Aphelion-Aerospace/psas-gps-rf-board/pubs/ethernet-circuits.pdf

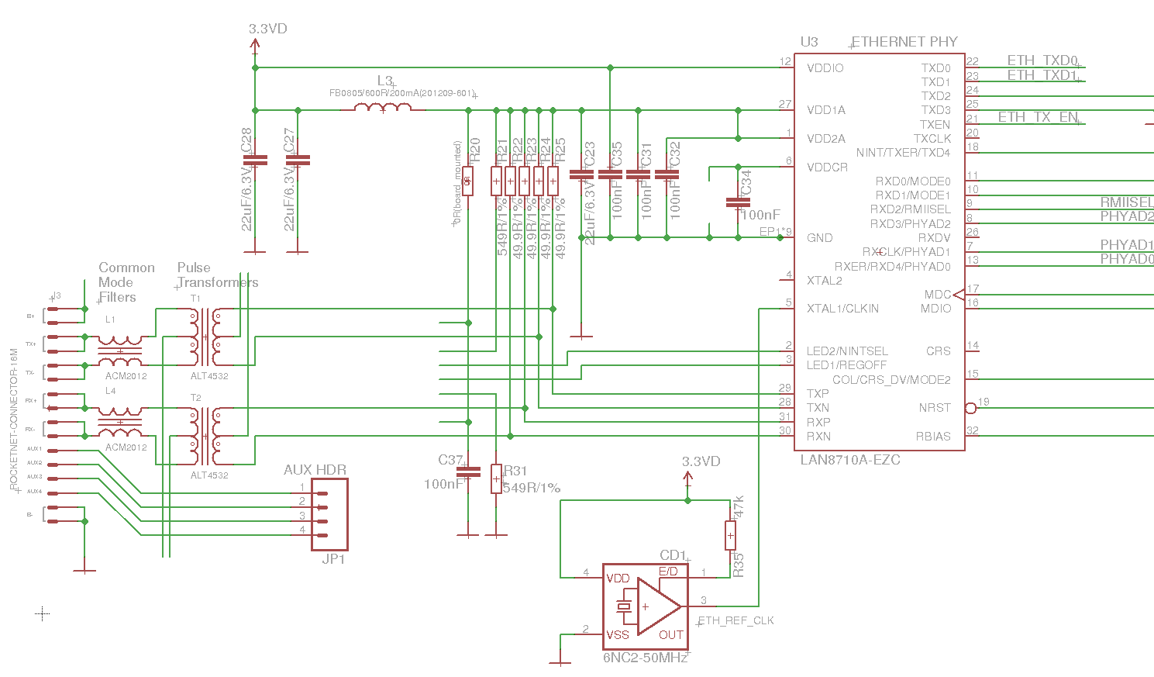
[picture p23: page 1]

GPS Board

Olimex E-407

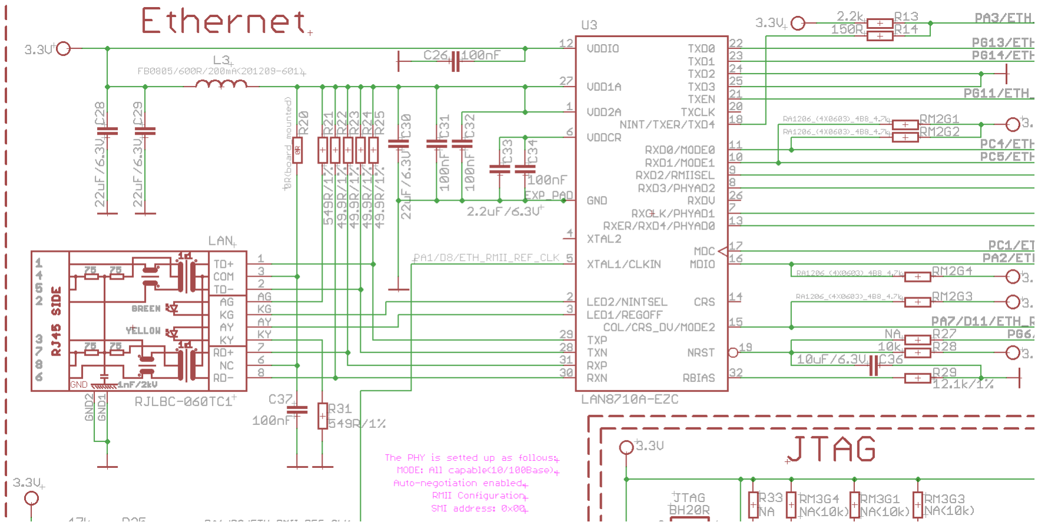
[picture p24: figure]

Rocketnet

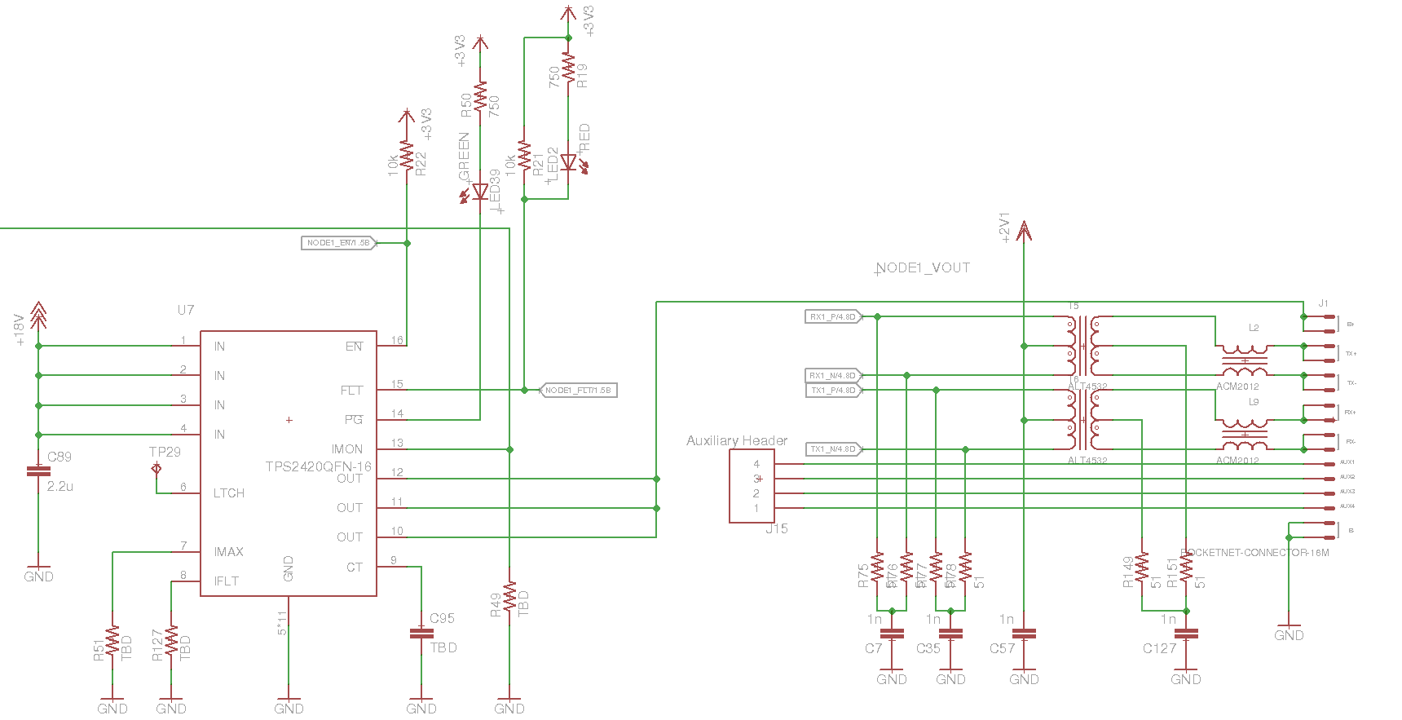
[picture p25: figure]
