Aphelion-Aerospace/psas-gps-rf-board/pubs/tcxo-7q-gps.pdf

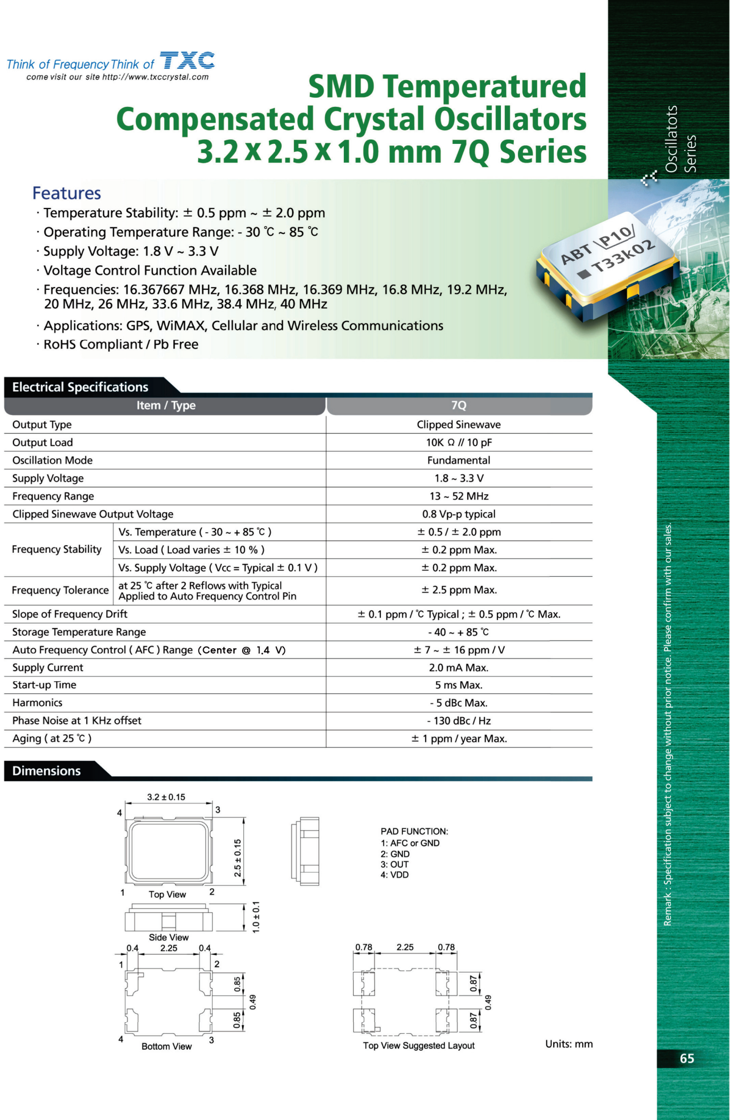
[picture p26: page 1]
