Aphelion-Aerospace/psas-gps-rf-board/pubs/con-samtec-swd-drawing.pdf

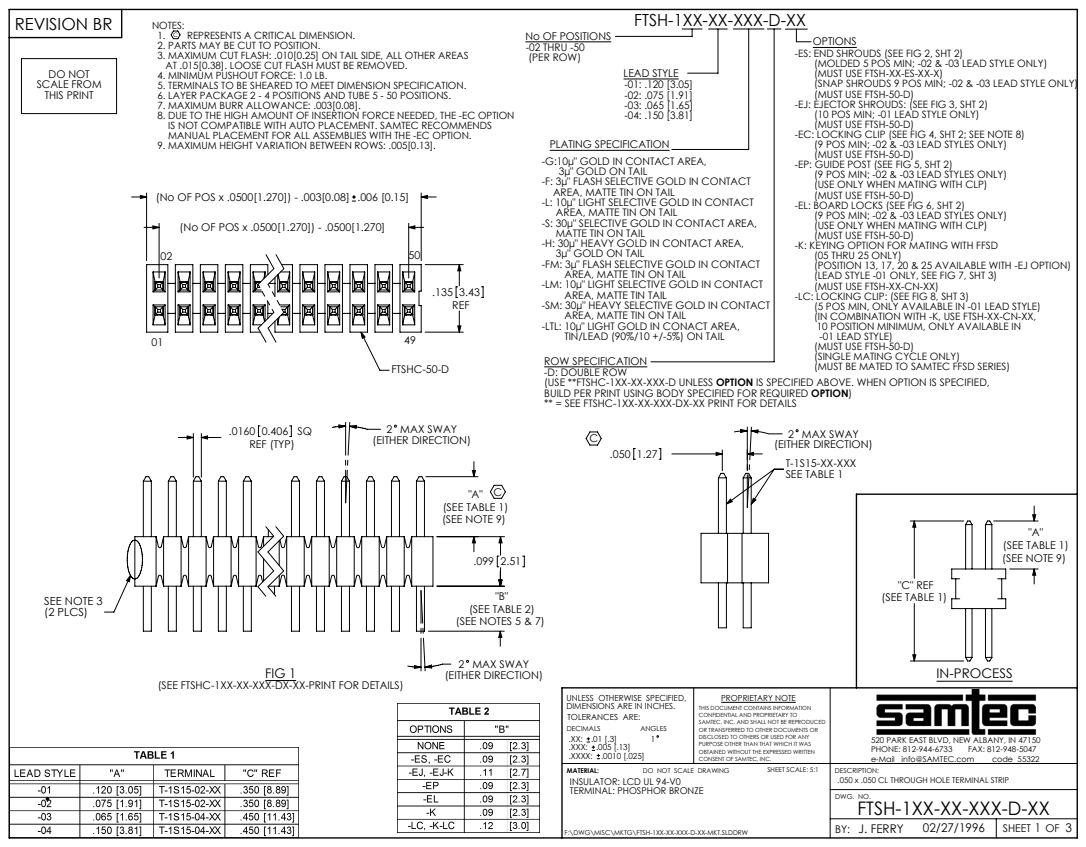
[picture p35: page 1]
DO NOT SCALE FROM THIS PRINT; LEAD STYLE -01: .120 [3.05] -02: .075 [1.91] -03: .065 [1.65] -04: .150 [3.81]; 2 MAX SWAY (EITHER DIRECTION) C; SEE TABLE 1; (SEE TABLE 1); "C" REF; (SEE NOTE 9); (SEE NOTES 5 & 7); (SEE TABLE 2); .0160 0.406 SQ REF (TYP); 2 MAX SWAY (EITHER DIRECTION); SEE NOTE 3 (2 PLCS); FIG 1; SHEET OF; J. FERRY 02/27/1996; SHEET SCALE: 5:1; PHONE: 812-944-6733; FAX: 812-948-5047; e-Mail info@SAMTEC.com; code 55322; REVISION BR

FTSH-1XX-XX-XXX-D-XX

NOTES:
1. REPRESENTS A CRITICAL DIMENSION.
2. PARTS MAY BE CUT TO POSITION.
3. MAXIMUM CUT FLASH: .010[0.25] ON TAIL SIDE, ALL OTHER AREAS
AT .015[0.38]. LOOSE CUT FLASH MUST BE REMOVED.
4. MINIMUM PUSHOUT FORCE: 1.0 LB.
5. TERMINALS TO BE SHEARED TO MEET DIMENSION SPECIFICATION.
6. LAYER PACKAGE 2 - 4 POSITIONS AND TUBE 5 - 50 POSITIONS.
7. MAXIMUM BURR ALLOWANCE: .003[0.08].
8. DUE TO THE HIGH AMOUNT OF INSERTION FORCE NEEDED, THE -EC OPTION
IS NOT COMPATIBLE WITH AUTO PLACEMENT. SAMTEC RECOMMENDS
MANUAL PLACEMENT FOR ALL ASSEMBLIES WITH THE -EC OPTION.
9. MAXIMUM HEIGHT VARIATION BETWEEN ROWS: .005[0.13].

No OF POSITIONS
-02 THRU -50
(PER ROW)

OPTIONS
-ES: END SHROUDS (SEE FIG 2, SHT 2)
(MOLDED 5 POS MIN; -02 & -03 LEAD STYLE ONLY)
(MUST USE FTSH-XX-ES-XX-X)
(SNAP SHROUDS 9 POS MIN; -02 & -03 LEAD STYLE ONLY)
(MUST USE FTSH-50-D)
-EJ: EJECTOR SHROUDS: (SEE FIG 3, SHT 2)
(10 POS MIN; -01 LEAD STYLE ONLY)
-EC: LOCKING CLIP (SEE FIG 4, SHT 2; SEE NOTE 8)
(9 POS MIN; -02 & -03 LEAD STYLES ONLY)
-EP: GUIDE POST (SEE FIG 5, SHT 2)
(USE ONLY WHEN MATING WITH CLP)
-EL: BOARD LOCKS (SEE FIG 6, SHT 2)
-K: KEYING OPTION FOR MATING WITH FFSD
(05 THRU 25 ONLY)
(POSITION 13, 17, 20 & 25 AVAILABLE WITH -EJ OPTION)
(LEAD STYLE -01 ONLY, SEE FIG 7, SHT 3)
(MUST USE FTSH-XX-CN-XX)
-LC: LOCKING CLIP: (SEE FIG 8, SHT 3)
(5 POS MIN, ONLY AVAILABLE IN -01 LEAD STYLE)
(IN COMBINATION WITH -K, USE FTSH-XX-CN-XX,
10 POSITION MINIMUM, ONLY AVAILABLE IN
-01 LEAD STYLE)
(SINGLE MATING CYCLE ONLY)
(MUST BE MATED TO SAMTEC FFSD SERIES)

PLATING SPECIFICATION
-G:10µ" GOLD IN CONTACT AREA,
3µ" GOLD ON TAIL
-F: 3µ" FLASH SELECTIVE GOLD IN CONTACT
AREA, MATTE TIN ON TAIL
-L: 10µ" LIGHT SELECTIVE GOLD IN CONTACT
-S: 30µ" SELECTIVE GOLD IN CONTACT AREA,
MATTE TIN ON TAIL
-H: 30µ" HEAVY GOLD IN CONTACT AREA,
-FM: 3µ" FLASH SELECTIVE GOLD IN CONTACT
-LM: 10µ" LIGHT SELECTIVE GOLD IN CONTACT
AREA, MATTE TIN TAIL
-SM: 30µ" HEAVY SELECTIVE GOLD IN CONTACT
-LTL: 10µ" LIGHT GOLD IN CONACT AREA,
TIN/LEAD (90%/10 +/-5%) ON TAIL
ROW SPECIFICATION
-D: DOUBLE ROW
(USE **FTSHC-1XX-XX-XXX-D UNLESS OPTION IS SPECIFIED ABOVE. WHEN OPTION IS SPECIFIED,
BUILD PER PRINT USING BODY SPECIFIED FOR REQUIRED OPTION)
** = SEE FTSHC-1XX-XX-XXX-DX-XX PRINT FOR DETAILS

(No OF POS x .0500[1.270]) - .003[0.08] .006 [0.15]

(No OF POS x .0500[1.270]) - .0500[1.270]

(SEE FTSHC-1XX-XX-XXX-DX-XX-PRINT FOR DETAILS)

UNLESS OTHERWISE SPECIFIED,
DIMENSIONS ARE IN INCHES.
TOLERANCES ARE:
.XXX: .005 [.13]
.XXXX: .0010 [.025]
MATERIAL:
INSULATOR: LCD UL 94-V0
TERMINAL: PHOSPHOR BRONZE

PROPRIETARY NOTE
THIS DOCUMENT CONTAINS INFORMATION
CONFIDENTIAL AND PROPRIETARY TO
SAMTEC, INC. AND SHALL NOT BE REPRODUCED
OR TRANSFERRED TO OTHER DOCUMENTS OR
DISCLOSED TO OTHERS OR USED FOR ANY
PURPOSE OTHER THAN THAT WHICH IT WAS
OBTAINED WITHOUT THE EXPRESSED WRITTEN
CONSENT OF SAMTEC, INC.

520 PARK EAST BLVD, NEW ALBANY, IN 47150
FTSH-1XX-XX-XXX-D-XX DWG. NO.

DO NOT SCALE DRAWING

DESCRIPTION:
.050 x .050 CL THROUGH HOLE TERMINAL STRIP

F:\DWG\MISC\MKTG\FTSH-1XX-XX-XXX-D-XX-MKT.SLDDRW

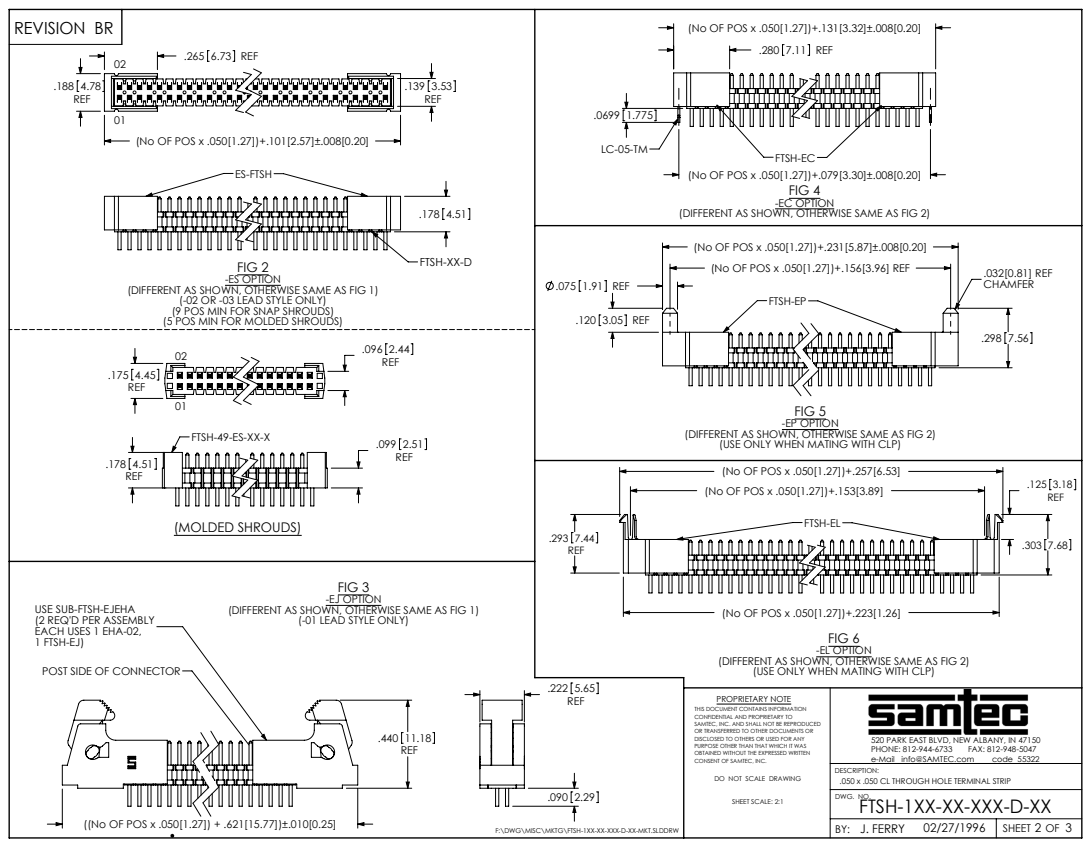
[picture p36: page 2]
(No OF POS x .050[1.27])+.101[2.57]±.008[0.20]; FIG 2 -ES OPTION; REF .178; (MOLDED SHROUDS); FIG 6 -EL OPTION; .032[0.81] REF; J. FERRY 02/27/1996; SHEET SCALE: 2:1; PHONE: 812-944-6733; FAX: 812-948-5047; e-Mail info@SAMTEC.com; code 55322

(No OF POS x .050[1.27])+.131[3.32]±.008[0.20]

(No OF POS x .050[1.27])+.079[3.30]±.008[0.20]

FIG 4 -EC OPTION (DIFFERENT AS SHOWN, OTHERWISE SAME AS FIG 2)

(No OF POS x .050[1.27])+.231[5.87]±.008[0.20]
(No OF POS x .050[1.27])+.156[3.96] REF

(DIFFERENT AS SHOWN, OTHERWISE SAME AS FIG 1)

(-02 OR -03 LEAD STYLE ONLY)
(9 POS MIN FOR SNAP SHROUDS)
(5 POS MIN FOR MOLDED SHROUDS)

FIG 5 -EP OPTION (DIFFERENT AS SHOWN, OTHERWISE SAME AS FIG 2) (USE ONLY WHEN MATING WITH CLP)

FTSH-49-ES-XX-X

(No OF POS x .050[1.27])+.257[6.53]
(No OF POS x .050[1.27])+.153[3.89]

FIG 3
-EJ OPTION
(-01 LEAD STYLE ONLY)

USE SUB-FTSH-EJEHA
(2 REQ'D PER ASSEMBLY
EACH USES 1 EHA-02,
1 FTSH-EJ)

(No OF POS x .050[1.27])+.223[1.26]

(DIFFERENT AS SHOWN, OTHERWISE SAME AS FIG 2)
(USE ONLY WHEN MATING WITH CLP)

POST SIDE OF CONNECTOR

PROPRIETARY NOTE
THIS DOCUMENT CONTAINS INFORMATION
CONFIDENTIAL AND PROPRIETARY TO
SAMTEC, INC. AND SHALL NOT BE REPRODUCED
OR TRANSFERRED TO OTHER DOCUMENTS OR
DISCLOSED TO OTHERS OR USED FOR ANY
PURPOSE OTHER THAN THAT WHICH IT WAS
OBTAINED WITHOUT THE EXPRESSED WRITTEN
CONSENT OF SAMTEC, INC.
DO NOT SCALE DRAWING

520 PARK EAST BLVD, NEW ALBANY, IN 47150

((No OF POS x .050[1.27]) + .621[15.77])±.010[0.25]

F:\DWG\MISC\MKTG\FTSH-1XX-XX-XXX-D-XX-MKT.SLDDRW

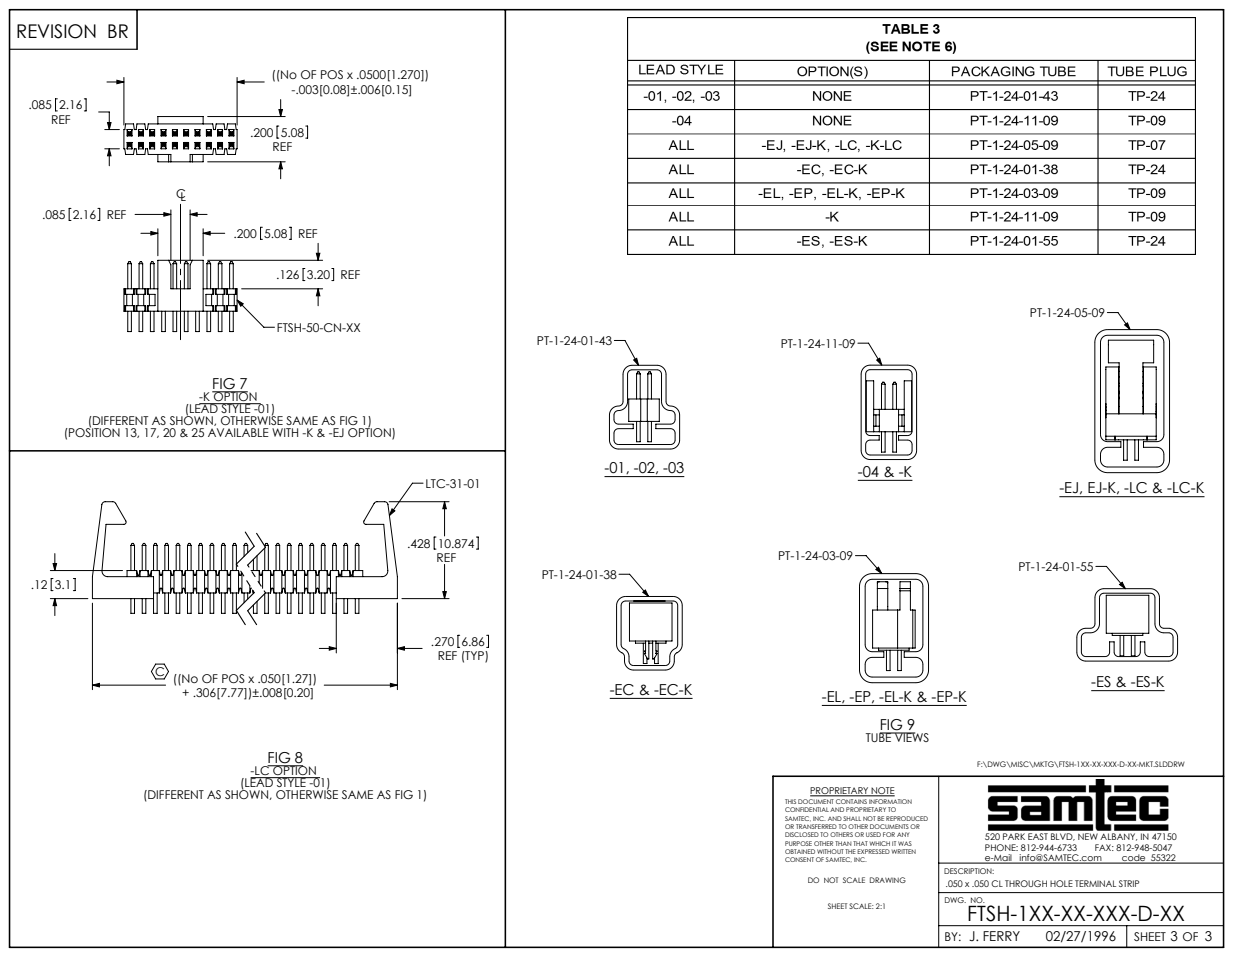
[picture p37: page 3]
FIG 7 -K OPTION (LEAD STYLE -01); ((No OF POS x .050[1.27]) + .306[7.77])±.008[0.20]; REF (TYP); FIG 8 -LC OPTION (LEAD STYLE -01); J. FERRY; SHEET SCALE: 2:1; PHONE: 812-944-6733; FAX: 812-948-5047; e-Mail info@SAMTEC.com; code 55322

((No OF POS x .0500[1.270])

FTSH-50-CN-XX

(DIFFERENT AS SHOWN, OTHERWISE SAME AS FIG 1)
(POSITION 13, 17, 20 & 25 AVAILABLE WITH -K & -EJ OPTION)

FIG 9
TUBE VIEWS

F:\DWG\MISC\MKTG\FTSH-1XX-XX-XXX-D-XX-MKT.SLDDRW

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

520 PARK EAST BLVD, NEW ALBANY, IN 47150
