Aphelion-Aerospace/psas-gps-rf-board/pubs/max2769/MAX2769-PACKAGE-21-0140.PDF

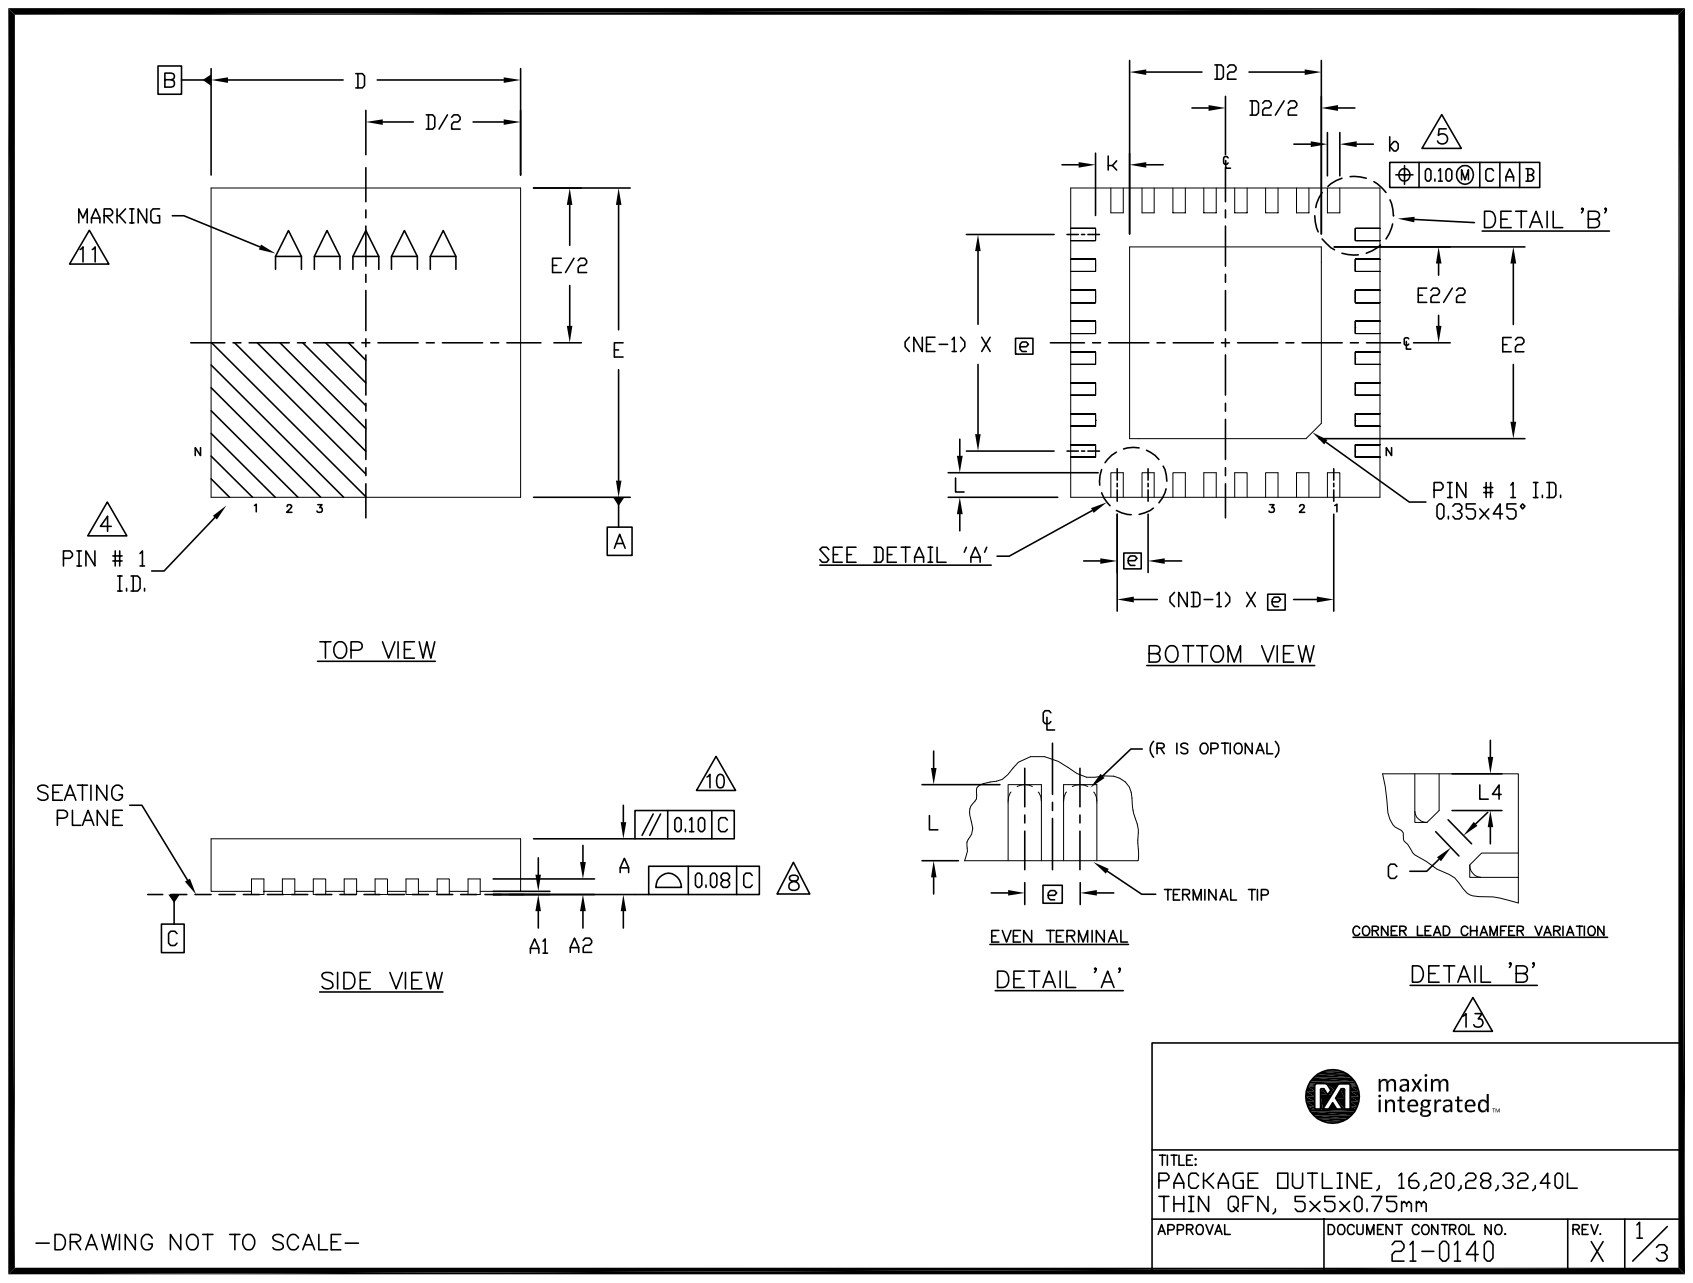
[picture p38: page 1]

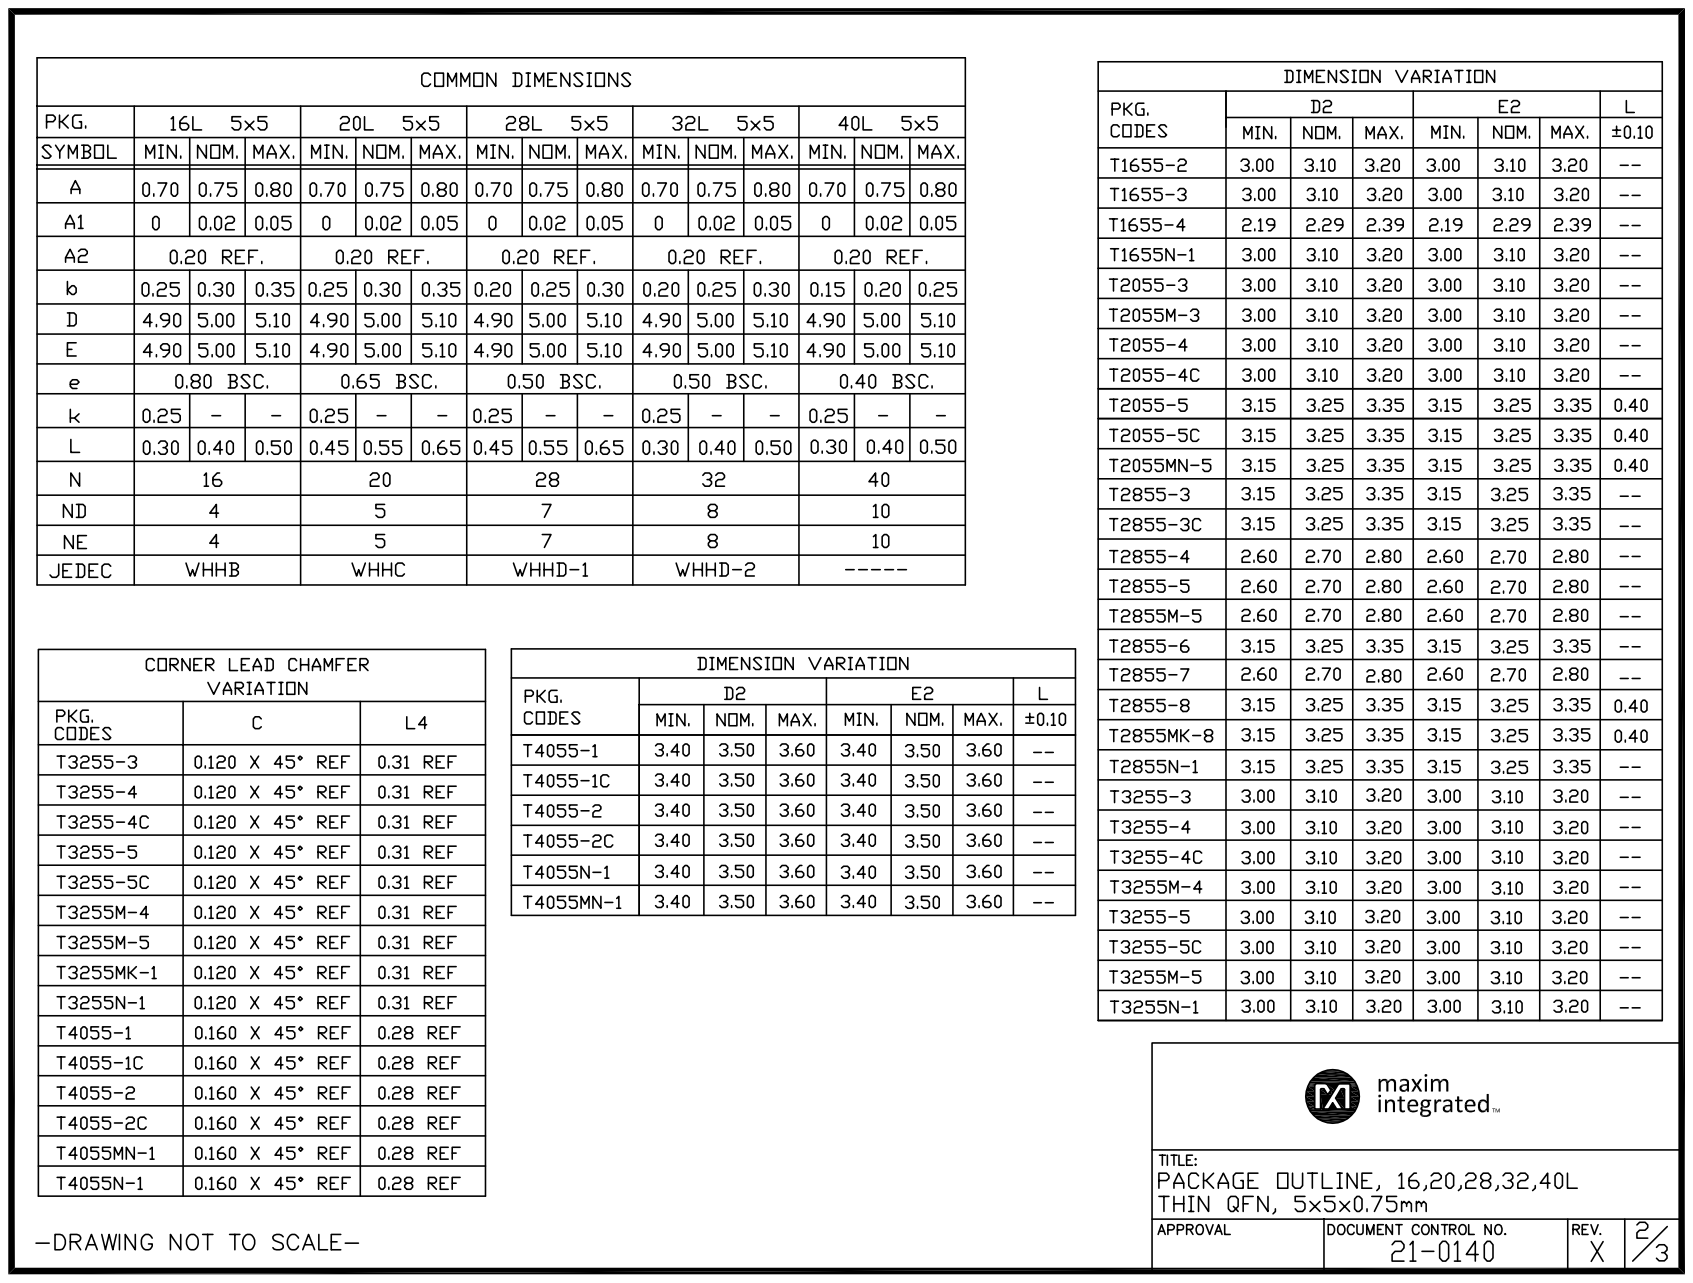
[picture p39: page 2]

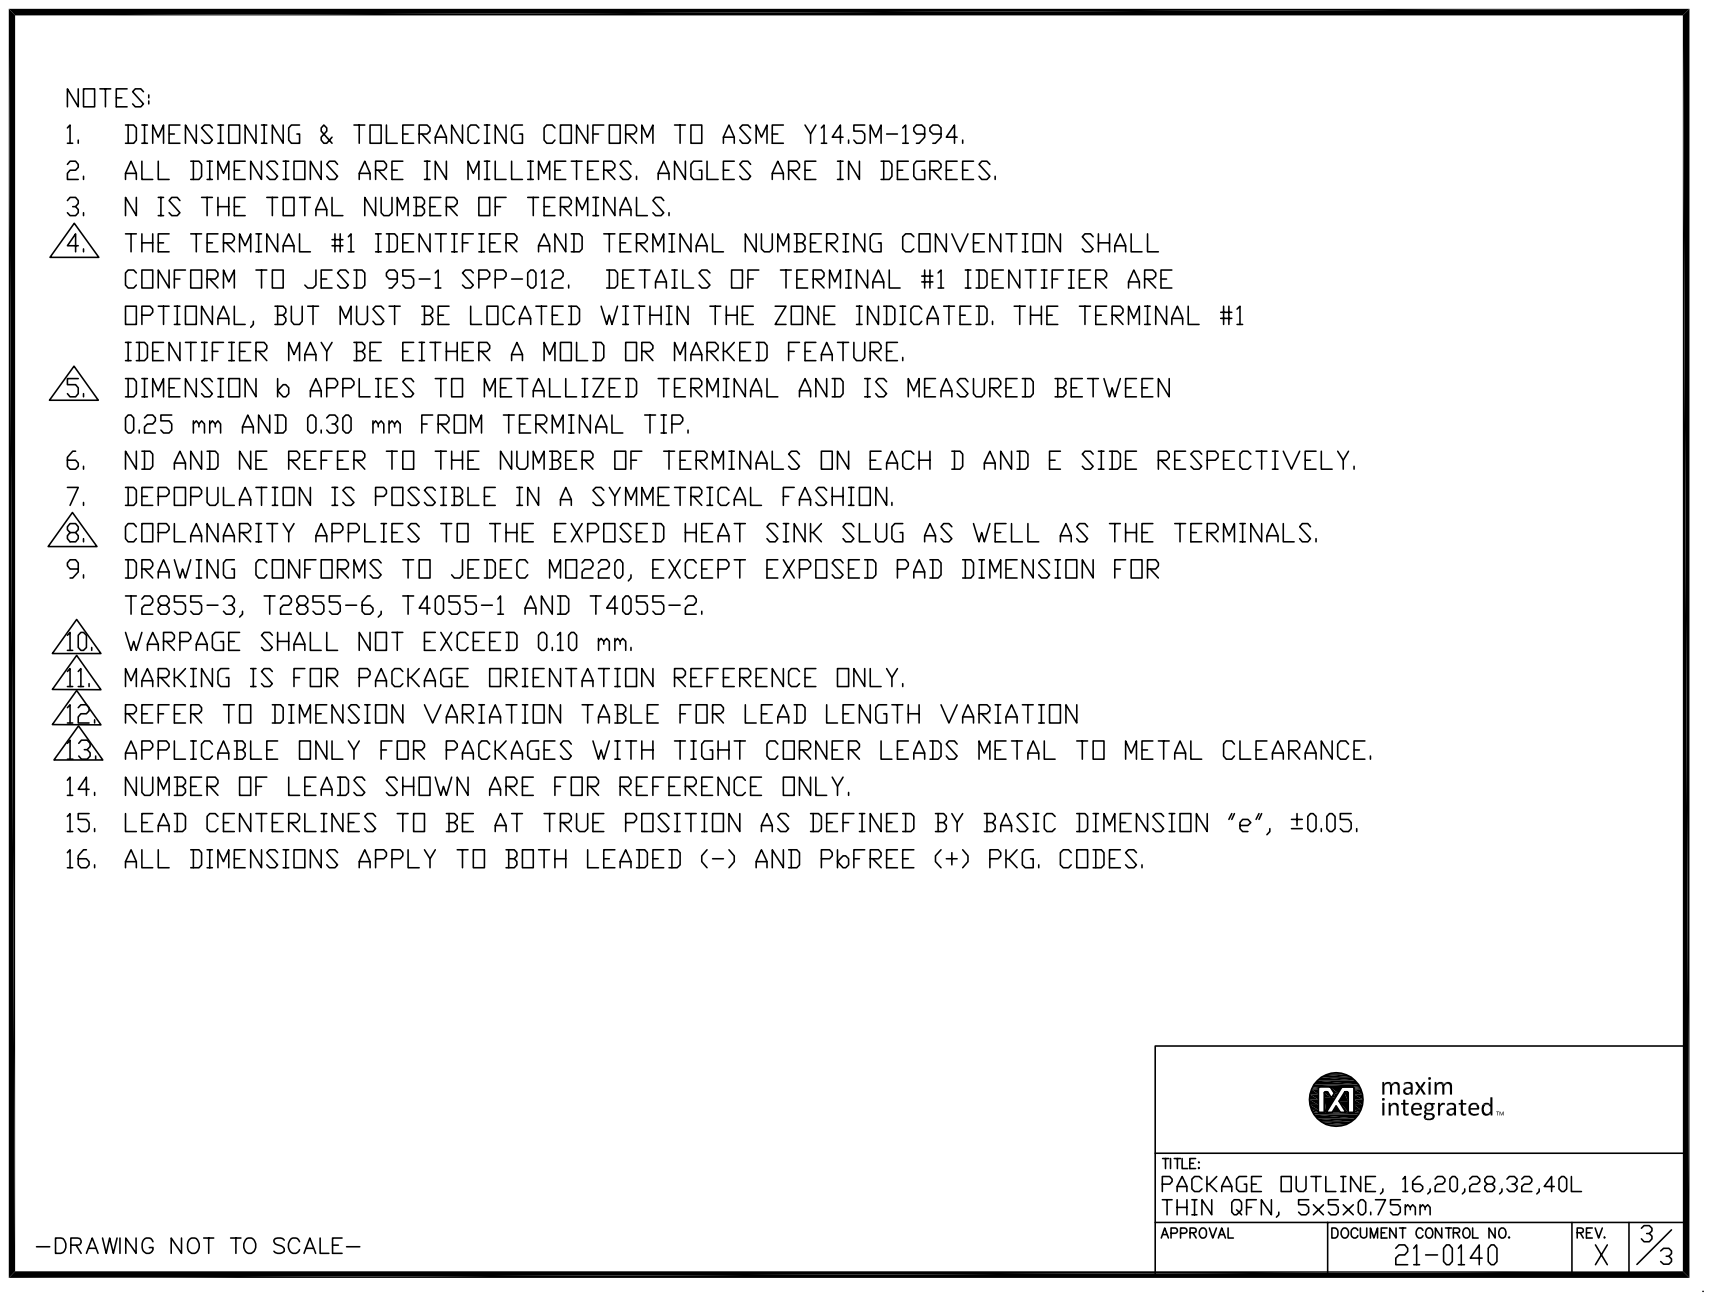
[picture p40: page 3]
