Aphelion-Aerospace/psas-gps-rf-board/pubs/max2769/MAX2769 FOOTPRINT 21-0140.PDF

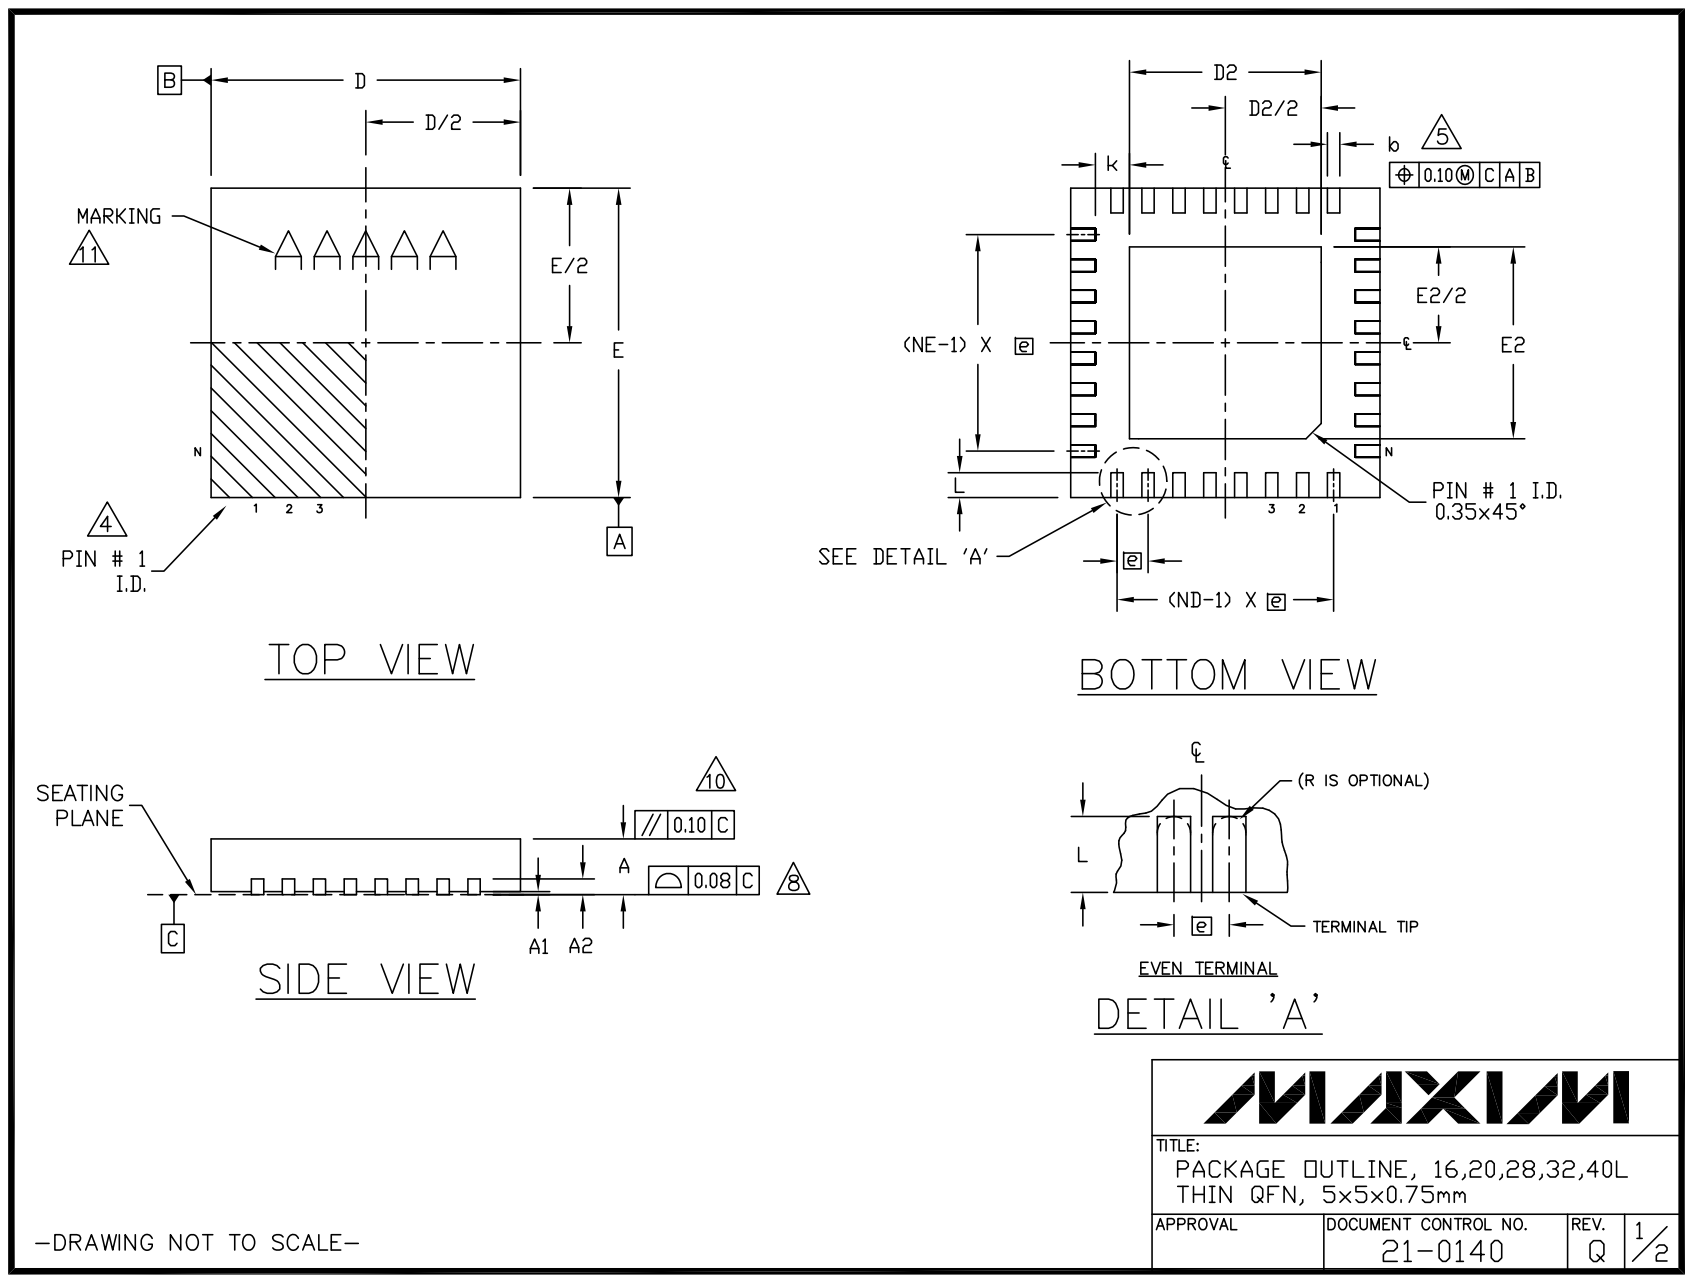
[picture p41: page 1]

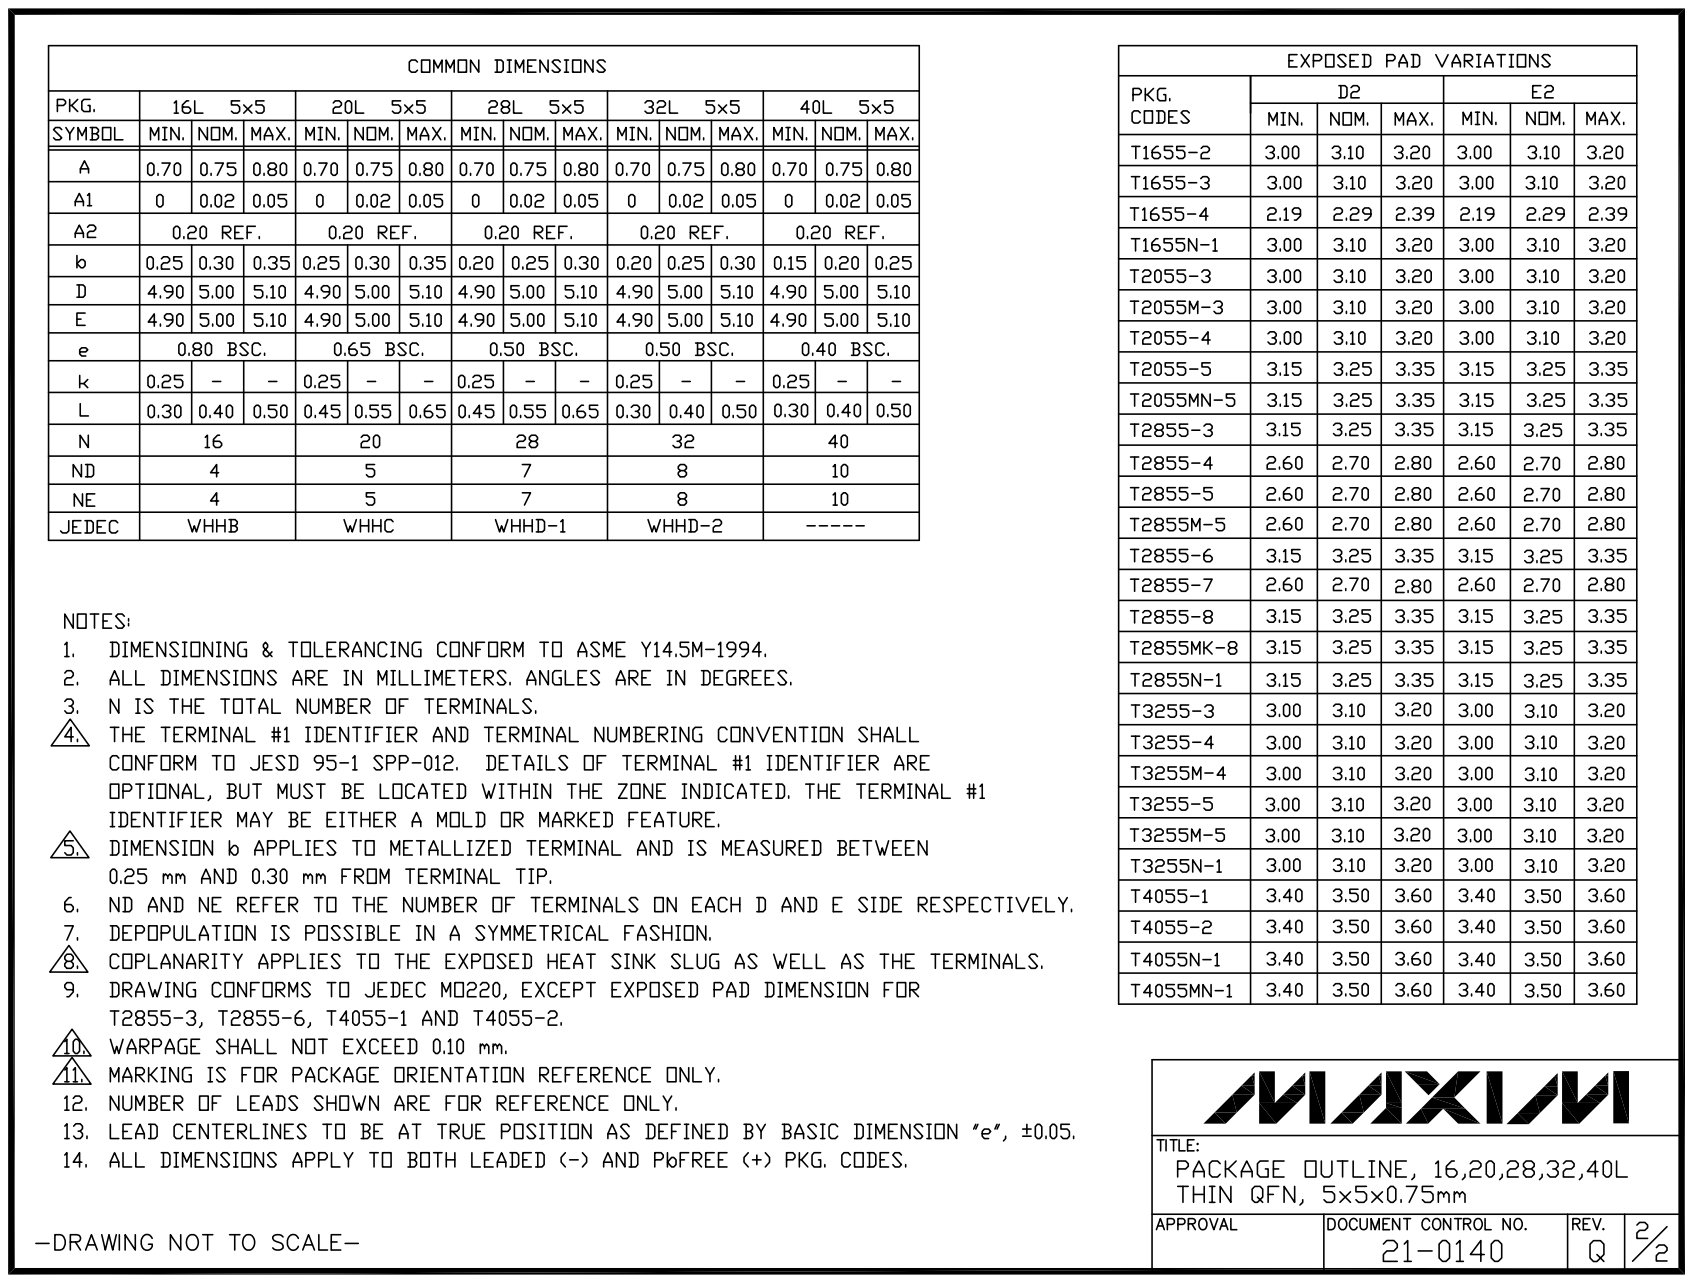
[picture p42: page 2]
