Aphelion-Aerospace/psas-gps-rf-board/pubs/max2769/MAX2769 FOOTPRINT 90-0023.PDF

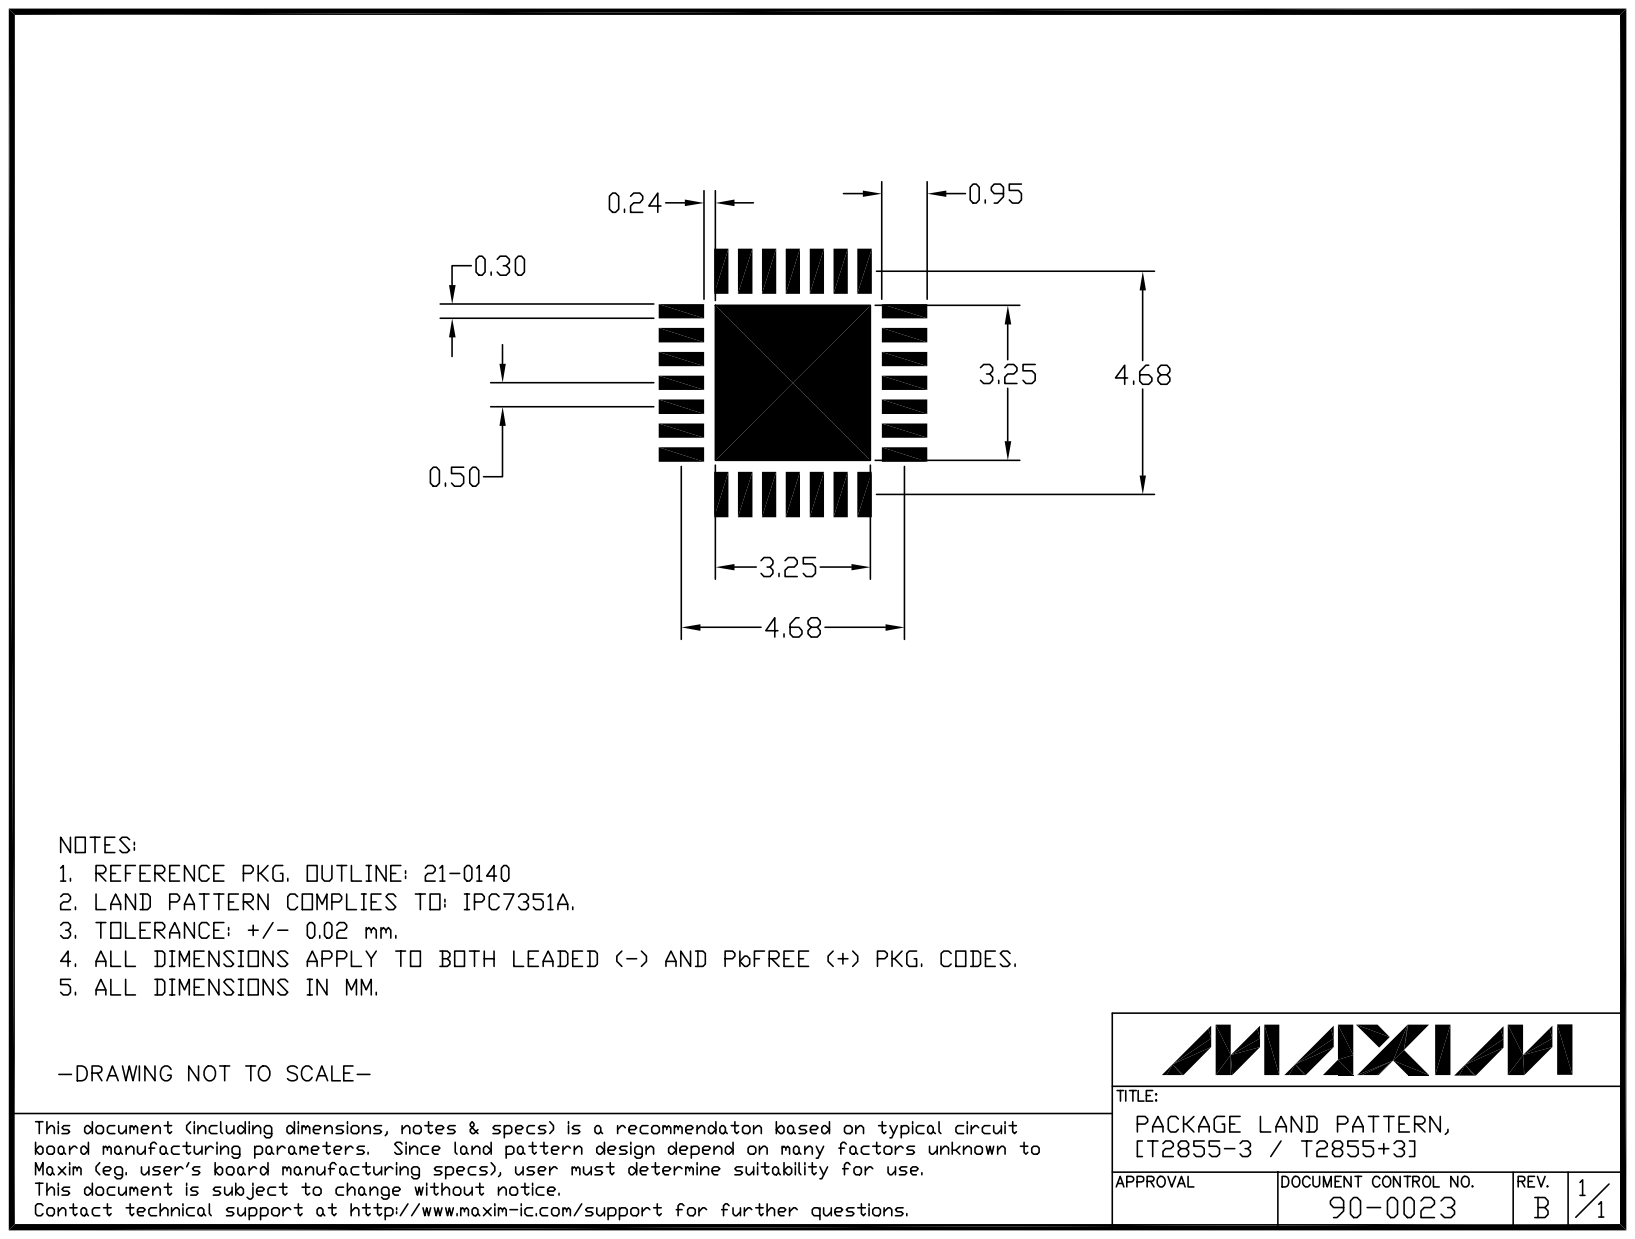
[picture p43: page 1]
